alexandreberg/SAPI_an_open_source_FEWS/docs/tests/notifications-m4-m6/images/03_predictions_php_overview.png

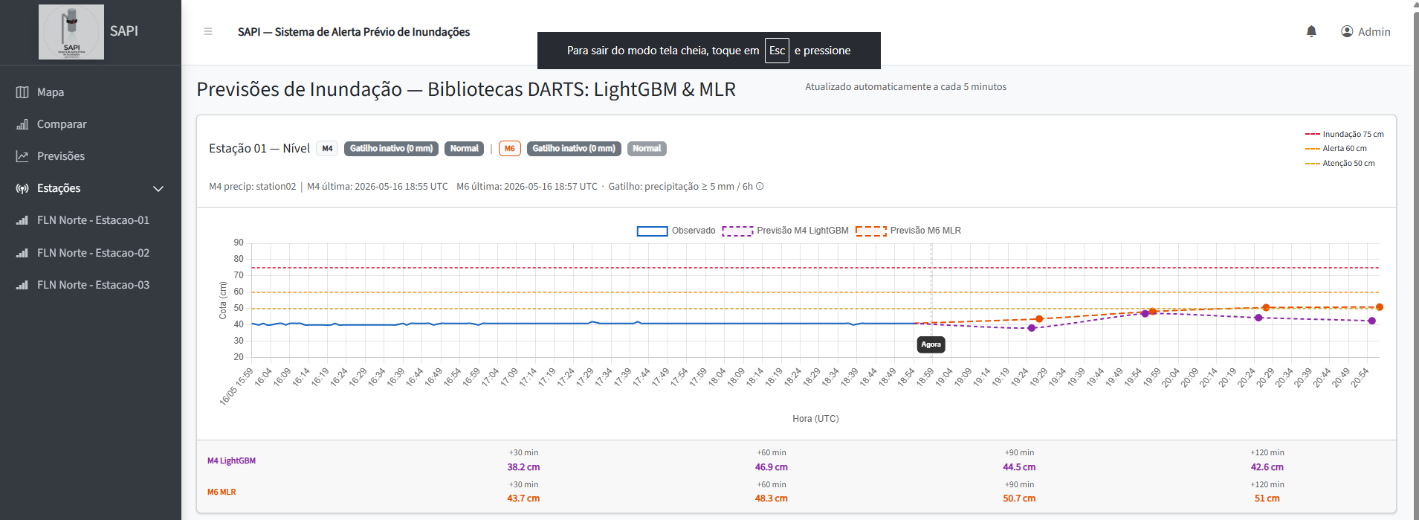
docs/tests/notifications-m4-m6/images/03_predictions_php_overview.png
