alexandreberg/SAPI_an_open_source_FEWS/hardware/lora-arduino-shield-v1.0/SAPI_LoRa_Arduino_Shield_V1.0-FC.png

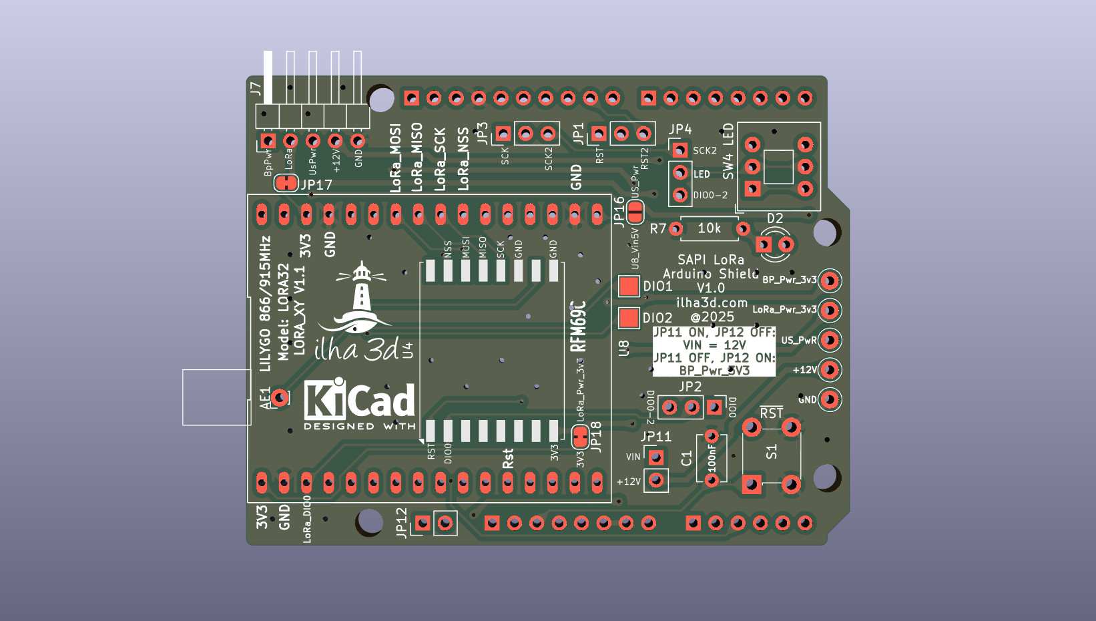
hardware/lora-arduino-shield-v1.0/SAPI_LoRa_Arduino_Shield_V1.0-FC.png
