alexandreberg/SAPI_an_open_source_FEWS/hardware/morpho-shield-v1.2/jlcpcb-02.11.2025.png

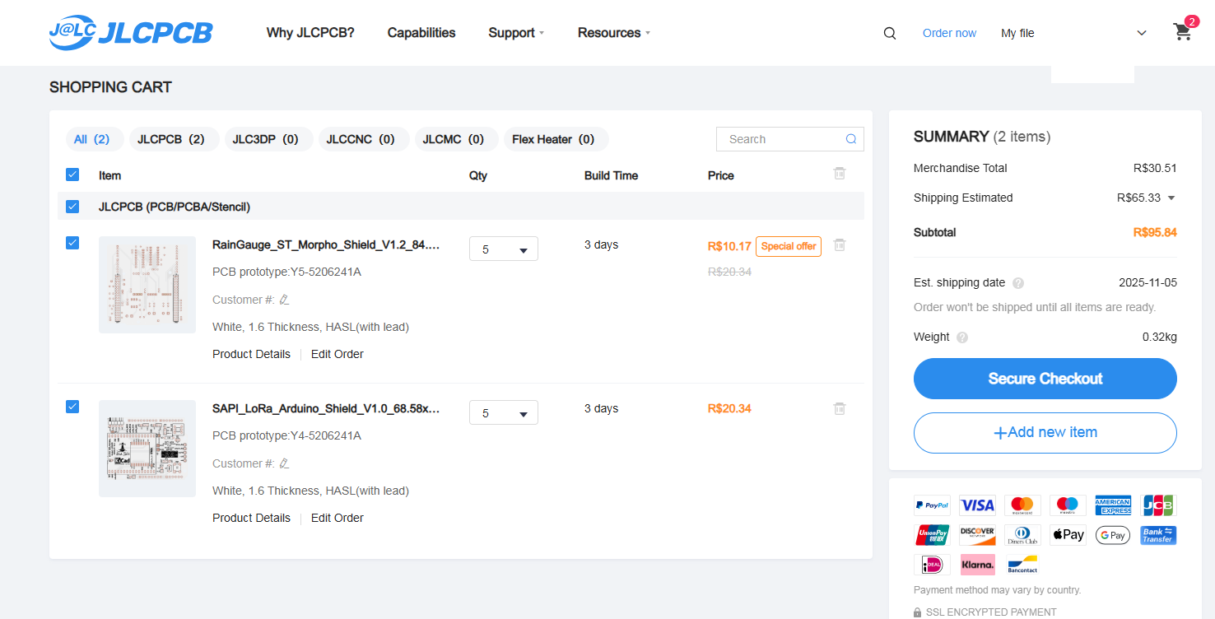
hardware/morpho-shield-v1.2/jlcpcb-02.11.2025.png
