alexandreberg/SAPI_an_open_source_FEWS/hardware/morpho-shield-v1.2/RainGauge_ST_Morpho_Shield_V1.2-BC-comp.png

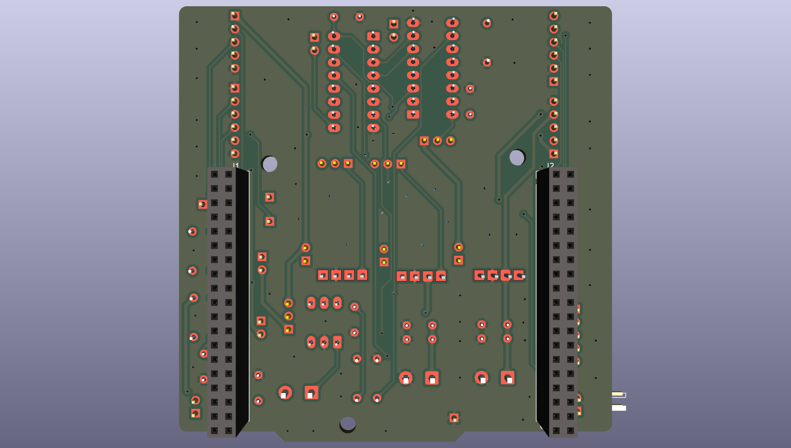
hardware/morpho-shield-v1.2/RainGauge_ST_Morpho_Shield_V1.2-BC-comp.png
