alexandreberg/SAPI_an_open_source_FEWS/webserver/public_html/sapi/assets/img/stations/station-1.jpg

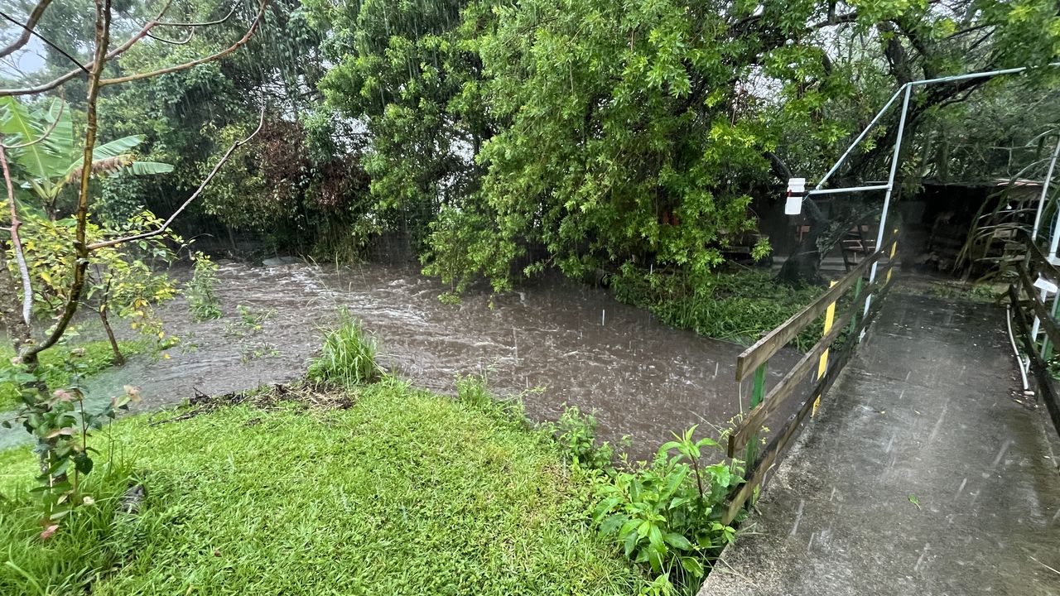
webserver/public_html/sapi/assets/img/stations/station-1.jpg
