alexandreberg/SAPI_an_open_source_FEWS/webserver/public_html/sapi/assets/img/stations/station-3.jpg

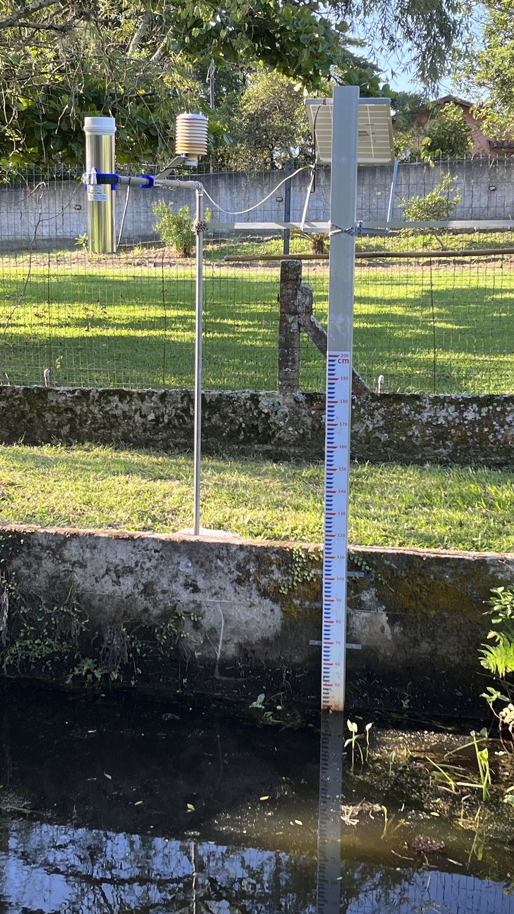
webserver/public_html/sapi/assets/img/stations/station-3.jpg
