alexandreberg/SAPI_an_open_source_FEWS/docs/tests/us-100/US-100_Trigger_Echo_mode_test-01/Data_test_US-100_Trigger_2026.Feb.15.md

## Test Results
Check that there is a problem. The US-100 in trigger mode is measuring at the maximum of 180cm.
Check for some code issue or it might be sensor specific problem?
I think it my be something with the filtering range routine.

**Note:** Bosch GLM 20 measurements corrected by -10.0 cm to account for instrument offset identified after testing.

* All measures in cm:
US-100 - Bosch (corrected)
28 - 25.7
48 - 44.0
68 - 63.1
98 - 89.7
126 - 115.3
152 - 139.3
180 - 164.2
-99 - 187.7
-99 - 209.3
-99 - 230.7
-99 - 248.9
-99 - 210.1
-99 - 200.1
-99 - 190.1
-99 - 187.7
-99 - 182.2
-99 - 175.9
-99 - 170.2
180 - 164.1
