alexandreberg/SAPI_an_open_source_FEWS/predictive-models/results_final_m4_lgbm/event_windows_v3.csv

event_num | peak_time | peak_cm | analysis_start | analysis_end | split_set | type | level | donor_pct | notes | exclusion | p24h_mm
1 | 2025-01-17 14:35:00 | 79 | 2025-01-16 21:45:00 | 2025-01-18 18:50:00 | train | flood | Alerta | 0.0 | subida máx. em 30 min: 7 cm |  | 192.6
2 | 2025-01-26 00:05:00 | 66 | 2025-01-25 17:55:00 | 2025-01-26 07:45:00 | train | flood | Atenção | 0.0 | subida máx. em 30 min: 6 cm |  | 52.5
3 | 2025-02-18 03:30:00 | 48 | 2025-02-17 22:10:00 | 2025-02-18 08:05:00 | train | flood | Normal | 0.0 | subida máx. em 30 min: 1 cm |  | 20.7
4 | 2025-04-10 19:35:00 | 98 | 2025-04-10 14:15:00 | 2025-04-11 22:55:00 | train | flash_flood | Inundação | 0.0 | subida máx. em 30 min: 34 cm |  | 5.3
5 | 2025-06-23 10:10:00 | 56 | 2025-06-23 03:55:00 | 2025-06-23 22:20:00 | train | flood | Normal | 0.0 | subida máx. em 30 min: 5 cm |  | 5.4
6 | 2025-06-26 22:25:00 | 58 | 2025-06-26 16:00:00 | 2025-06-27 09:00:00 | train | flood | Normal | 0.0 | subida máx. em 30 min: 6 cm |  | 6.9
7 | 2025-10-29 06:00:00 | 45 | 2025-10-29 00:55:00 | 2025-10-29 09:25:00 | train | flood | Normal | 0.0 | subida máx. em 30 min: 1 cm |  | 19.6
8 | 2025-12-09 15:00:00 | 163 | 2025-12-09 09:55:00 | 2025-12-10 18:35:00 | train | flash_flood | Inundação | 0.0 | subida máx. em 30 min: 78 cm |  | 31.5
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
32 | 2026-08-12 19:55:00 | 80 | 2026-08-12 11:40:00 | 2026-08-13 12:00:00 | test | flood | Alerta | 87.4 | subida máx. em 30 min: 9 cm; 87% da janela vem da E03 (Issue #225) |  | 48.6
33 | 2026-08-15 16:30:00 | 92 | 2026-08-13 14:55:00 | 2026-08-16 09:20:00 | test | flood | Inundação | 92.9 | subida máx. em 30 min: 11 cm; 93% da janela vem da E03 (Issue #225) |  | 56.5
34 | 2026-08-29 15:55:00 | 77 | 2026-08-29 10:30:00 | 2026-08-30 07:50:00 | test | flood | Alerta | 0.0 | subida máx. em 30 min: 12 cm |  | 22.0
35 | 2026-09-01 02:20:00 | 101 | 2026-08-30 09:10:00 | 2026-09-01 20:25:00 | test | flood | Inundação | 0.0 | subida máx. em 30 min: 11 cm |  | 54.7
