alexandreberg/SAPI_an_open_source_FEWS/predictive-models/results_final_m6_mlr/README.md

# results_final_m6_mlr

**Final validated backtesting for Model 6 — LinearRegressionModel / MLR (Darts).**

Previously named `real_data_m6_mlr/`. Contains the M6 backtest results and the controlled
M4 vs M6 comparison (same pipeline, same events, same thresholds — only the learning
algorithm differs) used in the dissertation methodology.

## Scripts

| Script | Purpose |
|---|---|
| `config.py` | Hyper-parameters — identical to `../results_final_m4_lgbm/config.py` and mirrored in `production_m6/config_production_m6.py`; `EVENTS_CSV` points to the shared `../results_final_m4_lgbm/event_windows_v3.csv` |
| `real_utils.py` | Data loading (identical pipeline to M4) |
| `01_model6_mlr_continuous.py` | Continuous backtest over the full record (2024-12-30 → 2026-09-12, ~21 months); auto-detects 25 Atenção-crossing periods |
| `02_precip_gate_m6.py` | Gate sensitivity (5/10/15 mm) |
| `03_compare_m4_m6.py` | M4 vs M6 comparison plot and metrics (`compare_m4_vs_m6.*`) |
| `04_lead_time_m6.py` | Lead time analysis by alert level |
| `05_rmse_per_event.py` | RMSE per test event, M4 vs M6 (`rmse_per_event*`) |
| `06_compare_fullsim.py` | RMSE over the full continuous simulation (`compare_m4_vs_m6_fullsim.*`) |

## Output images (`output/`)

**Summary M4-vs-M6 comparison:**
- `compare_m4_vs_m6.png` — RMSE per horizon and alert metrics (recall / false positives)
  at 60/75/90 cm, gate 5 mm / 6 h, persistence of 3 steps. **Read the caveat below.**
- `compare_m4_vs_m6_fullsim.png` — RMSE over the full continuous simulation, same caveat
- `lead_time_comparison_m4_vs_m6.png` — advance warning time by level, per test event
  (E28–E37) and horizon
- `rmse_per_event_m4_vs_m6.png` — RMSE per test event

**Per model:**
- `lead_time_atencao_m6.png`, `lead_time_alerta_m6.png`, `lead_time_inundacao_m6.png`
- `alert_timeline_atencao.png` / `alert_timeline_alerta.png` / `alert_timeline_inundacao.png`
- `precip_gate_timeline_[level]_gate[5/10/15]mm.png` — 9 images (gate analysis)

**Per auto-detected period** (from the continuous backtest, distinct from the 37 catalogued
episodes in `event_windows_v3.csv` — see Issue #213):
- `event_detected_001.png` … `event_detected_025.png` — numbered identically to
  `results_final_m4_lgbm/output/`'s plots (same observed level, threshold and merge gap drive
  `detect_flood_periods()` for both models). See the
  [period → catalogued event mapping table](../results_final_m4_lgbm/README.md#auto-detected-period--catalogued-event-mapping)
  in the M4 README for which `NNN` corresponds to which `Exx`.

## Caveat — which numbers are the published ones

`compare_m4_vs_m6.png` and `compare_m4_vs_m6_fullsim.png` compute the RMSE over **every step of
the record**, so they mix the training period (~79 % of the record, where the flexible M4 fits
much better) with the test period, and their alert counts include the training events. They do
**not** reproduce the dissertation's RMSE table, which reports the **out-of-sample** (test,
from 2026-05-01) and in-sample values separately, nor its test-only detection table. The
`lead_time_comparison_m4_vs_m6.png` figure, in contrast, covers the test events only.
Any claim about relative model performance must use the out-of-sample numbers in
the dissertation (authoritative) or the audit report generated by
`../plot_events_audit_pdf.py` (`../output_audit/auditoria_eventos_A3.pdf`).

## Documentation

- ~~`model6_comparison_pt-BR.md` / `.pdf`~~ — archived in the development repository on 2026-09-12:
  the deck dates from 2026-05-25 and still cites the 50/60/75 cm thresholds and the v2
  catalogue. Current numbers are in the
  dissertation and the audit report.

## Related

- M4 results: `../results_final_m4_lgbm/`
- Production config: `../production_m6/config_production_m6.py`
