alexandreberg/SAPI_an_open_source_FEWS/docs/tests/us-100/US-100_Serial_mode_test-02/Test-02-readings.md

## US-100 Serial Mode Measurement Test-02
Repeated test with US-100 in Serial mode in the new environment (dame pictures used in trigger mode), only with jumper inserted

**Note:** Bosch GLM 20 measurements corrected by -10.0 cm to account for instrument offset identified after testing.

* All measurements are in cm.

US-100 | Bosch (corrected)
27 | 24.0
43 | 39.9
58 | 54.0
71 | 66.2
90 | 84.7
107 | 101.1
121 | 113.9
139 | 130.8
159 | 148.7
175 | 163.7
197 | 183.4
222 | 207.2
243 | 225.9
268 | 249.4
294 | 274.1
315 | 292.7
333 | 309.4
355 | 329.0
371 | 344.7
395 | 367.1
-99 | 385.6
439 | 406.0
-99 | 419.0
-99 | 437.1
-99 | 451.3
-99 | 427.7
435 | 402.0
-99 | 391.4
408 | 378.6
396 | 367.3
385 | 356.7
366 | 339.5
348 | 322.7
328 | 304.3
310 | 288.3
285 | 265.2
265 | 247.0
244 | 227.2
223 | 207.3
201 | 187.9
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

Repeat the analysis from the first test in serial mode to this one and check if the results are consistent. After that create the report.
