alexandreberg/SAPI_an_open_source_FEWS/predictive-models/results_final_m4_lgbm/output/alert_analysis.csv

threshold_name | threshold_cm | debounce_steps | debounce_min | VP | FP | FN | VN | precision | recall | F1
Atenção | 60 | 1 | 5 | 18 | 25 | 0 | 169516 | 0.419 | 1.0 | 0.59
Atenção | 60 | 2 | 10 | 18 | 14 | 0 | 169603 | 0.562 | 1.0 | 0.72
Atenção | 60 | 3 | 15 | 18 | 9 | 0 | 169664 | 0.667 | 1.0 | 0.8
Alerta | 75 | 1 | 5 | 11 | 3 | 0 | 173126 | 0.786 | 1.0 | 0.88
Alerta | 75 | 2 | 10 | 11 | 3 | 0 | 173174 | 0.786 | 1.0 | 0.88
Alerta | 75 | 3 | 15 | 10 | 3 | 1 | 173213 | 0.769 | 0.909 | 0.833
Inundação | 90 | 1 | 5 | 6 | 0 | 1 | 175329 | 1.0 | 0.857 | 0.923
Inundação | 90 | 2 | 10 | 6 | 0 | 1 | 175343 | 1.0 | 0.857 | 0.923
Inundação | 90 | 3 | 15 | 6 | 0 | 1 | 175356 | 1.0 | 0.857 | 0.923
