alexandreberg/SAPI_an_open_source_FEWS/predictive-models/results_final_m4_lgbm/output/lead_time_summary_m4.csv

event_num | peak_cm | threshold_name | threshold_cm | occurrence | n_occurrences | t_obs | at_window_start | search_start | search_end | fire_30min | lead_time_30min | active_30min | fire_60min | lead_time_60min | active_60min | fire_90min | lead_time_90min | active_90min | fire_120min | lead_time_120min | active_120min
28 | 60.0 | Atenção | 60 | 1 | 1 | 2026-06-20 21:30:00 | False | 2026-06-20 18:30:00 | 2026-06-20 23:30:00 |  |  | False |  |  | False | 2026-06-20 21:15:00 | 15.0 | False | 2026-06-20 20:40:00 | 50.0 | False
29 | 65.0 | Atenção | 60 | 1 | 1 | 2026-06-30 09:55:00 | False | 2026-06-30 06:55:00 | 2026-06-30 19:30:00 | 2026-06-30 10:10:00 | -15.0 | False | 2026-06-30 10:10:00 | -15.0 | False | 2026-06-30 09:45:00 | 10.0 | False | 2026-06-30 09:30:00 | 25.0 | False
30 | 61.0 | Atenção | 60 | 1 | 1 | 2026-07-01 12:15:00 | False | 2026-07-01 09:15:00 | 2026-07-01 18:45:00 | 2026-07-01 13:35:00 | -80.0 | False |  |  | False |  |  | False |  |  | False
31 | 97.0 | Atenção | 60 | 1 | 1 | 2026-07-11 12:00:00 | False | 2026-07-11 09:00:00 | 2026-07-12 13:40:00 | 2026-07-11 12:05:00 | -5.0 | False | 2026-07-11 12:05:00 | -5.0 | False | 2026-07-11 11:55:00 | 5.0 | False | 2026-07-11 11:50:00 | 10.0 | False
32 | 80.0 | Atenção | 60 | 1 | 1 | 2026-08-12 16:30:00 | False | 2026-08-12 13:30:00 | 2026-08-13 05:50:00 | 2026-08-12 16:30:00 | 0.0 | False | 2026-08-12 16:25:00 | 5.0 | False | 2026-08-12 16:30:00 | 0.0 | False | 2026-08-12 16:25:00 | 5.0 | False
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
37 | 100.0 | Inundação | 90 | 1 | 1 | 2026-09-11 16:25:00 | False | 2026-09-11 13:25:00 | 2026-09-11 21:50:00 | 2026-09-11 17:15:00 | -50.0 | False |  |  | False |  |  | False |  |  | False
