alexandreberg/SAPI_an_open_source_FEWS/predictive-models/results_final_m4_lgbm/output/precip_gate_analysis.csv

threshold_name | threshold_cm | gate_hours | gate_mm | debounce_steps | debounce_min | VP | FP | FN | VN | precision | recall | F1
Atenção | 60 | 6 | 0 | 1 | 5 | 18 | 25 | 0 | 169516 | 0.419 | 1.0 | 0.59
Atenção | 60 | 6 | 0 | 2 | 10 | 18 | 14 | 0 | 169603 | 0.562 | 1.0 | 0.72
Atenção | 60 | 6 | 0 | 3 | 15 | 18 | 9 | 0 | 169664 | 0.667 | 1.0 | 0.8
Alerta | 75 | 6 | 0 | 1 | 5 | 11 | 3 | 0 | 173126 | 0.786 | 1.0 | 0.88
Alerta | 75 | 6 | 0 | 2 | 10 | 11 | 3 | 0 | 173174 | 0.786 | 1.0 | 0.88
Alerta | 75 | 6 | 0 | 3 | 15 | 10 | 3 | 1 | 173213 | 0.769 | 0.909 | 0.833
Inundação | 90 | 6 | 0 | 1 | 5 | 6 | 0 | 1 | 175329 | 1.0 | 0.857 | 0.923
Inundação | 90 | 6 | 0 | 2 | 10 | 6 | 0 | 1 | 175343 | 1.0 | 0.857 | 0.923
Inundação | 90 | 6 | 0 | 3 | 15 | 6 | 0 | 1 | 175356 | 1.0 | 0.857 | 0.923
Atenção | 60 | 6 | 5 | 1 | 5 | 18 | 8 | 0 | 170215 | 0.692 | 1.0 | 0.818
Atenção | 60 | 6 | 5 | 2 | 10 | 18 | 2 | 0 | 170277 | 0.9 | 1.0 | 0.947
Atenção | 60 | 6 | 5 | 3 | 15 | 18 | 0 | 0 | 170321 | 1.0 | 1.0 | 1.0
Alerta | 75 | 6 | 5 | 1 | 5 | 11 | 0 | 0 | 173188 | 1.0 | 1.0 | 1.0
Alerta | 75 | 6 | 5 | 2 | 10 | 11 | 0 | 0 | 173232 | 1.0 | 1.0 | 1.0
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
