alexandreberg/SAPI_an_open_source_FEWS/predictive-models/results_final_m6_mlr/output/compare_m4_vs_m6_fullsim.csv

horizonte_min | REQM_M4_LightGBM_cm | REQM_M6_MLR_cm
30 | 1.04 | 0.974
60 | 1.469 | 1.528
90 | 1.704 | 1.948
120 | 1.909 | 2.259
