alexandreberg/SAPI_an_open_source_FEWS/docs/tests/us-100/US-100_Serial_mode_test-01/US-100_Serial_Mode_Test-04.JPG

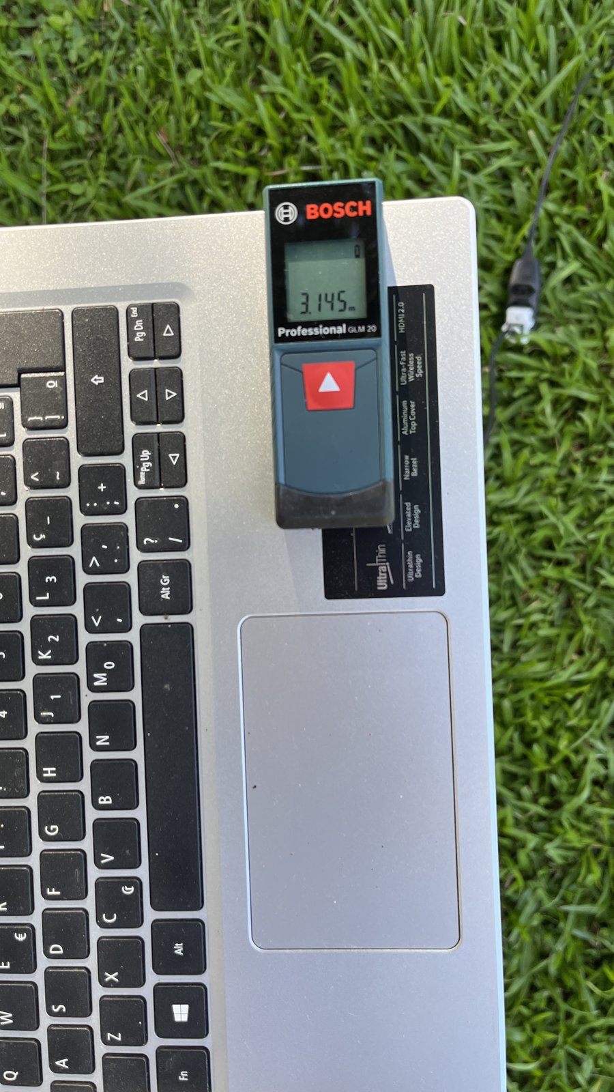
docs/tests/us-100/US-100_Serial_mode_test-01/US-100_Serial_Mode_Test-04.JPG
