alexandreberg/SAPI_an_open_source_FEWS/docs/tests/us-100/US-100_Serial_mode_test-04/images/IMG_3337.JPG

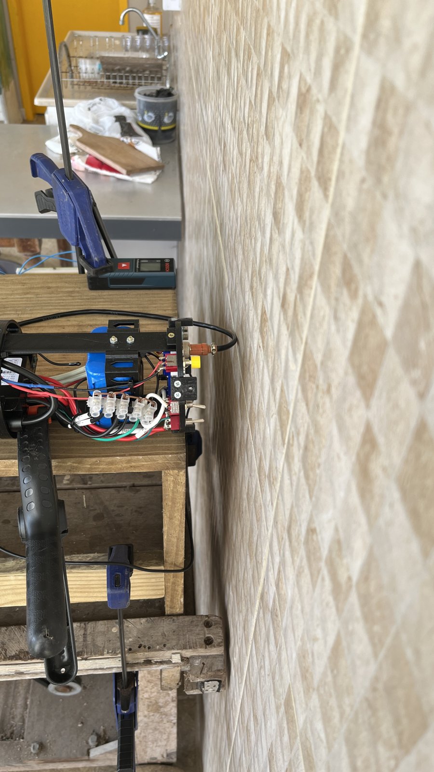
docs/tests/us-100/US-100_Serial_mode_test-04/images/IMG_3337.JPG
