alexandreberg/SAPI_an_open_source_FEWS/predictive-models/results_final_m4_lgbm/output/alert_timeline_atencao.png

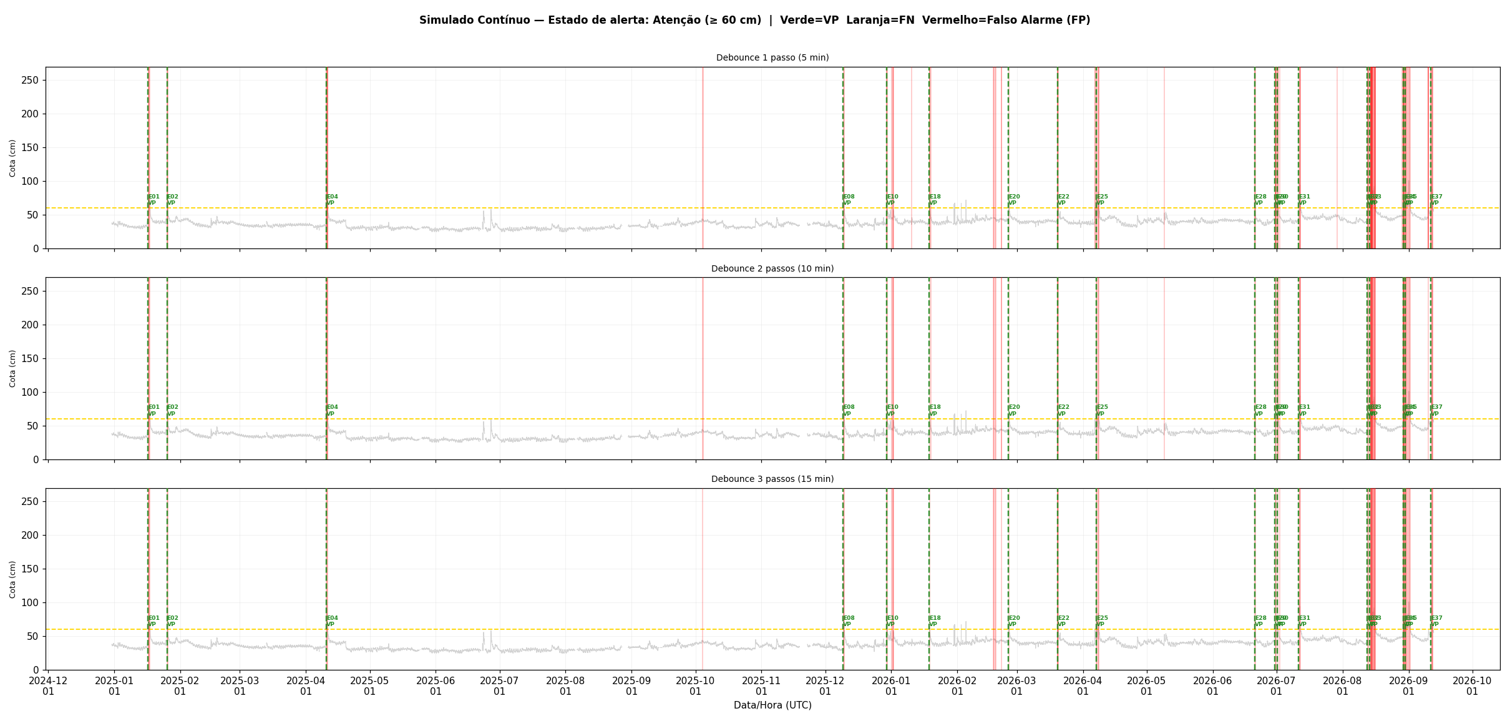
predictive-models/results_final_m4_lgbm/output/alert_timeline_atencao.png
