alexandreberg/SAPI_an_open_source_FEWS/predictive-models/results_final_m4_lgbm/output/event_detected_006.png

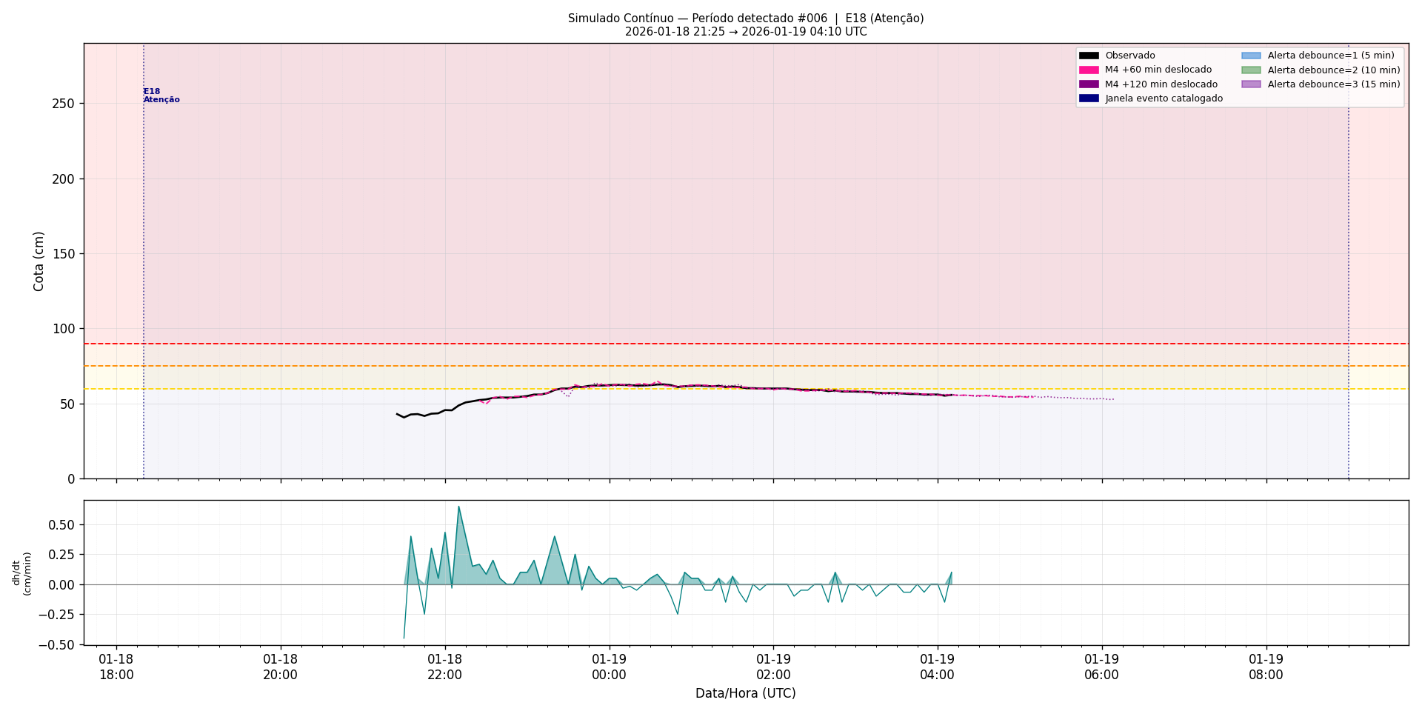
predictive-models/results_final_m4_lgbm/output/event_detected_006.png
