alexandreberg/SAPI_an_open_source_FEWS/predictive-models/results_final_m4_lgbm/output/lead_time_alerta_m4.png

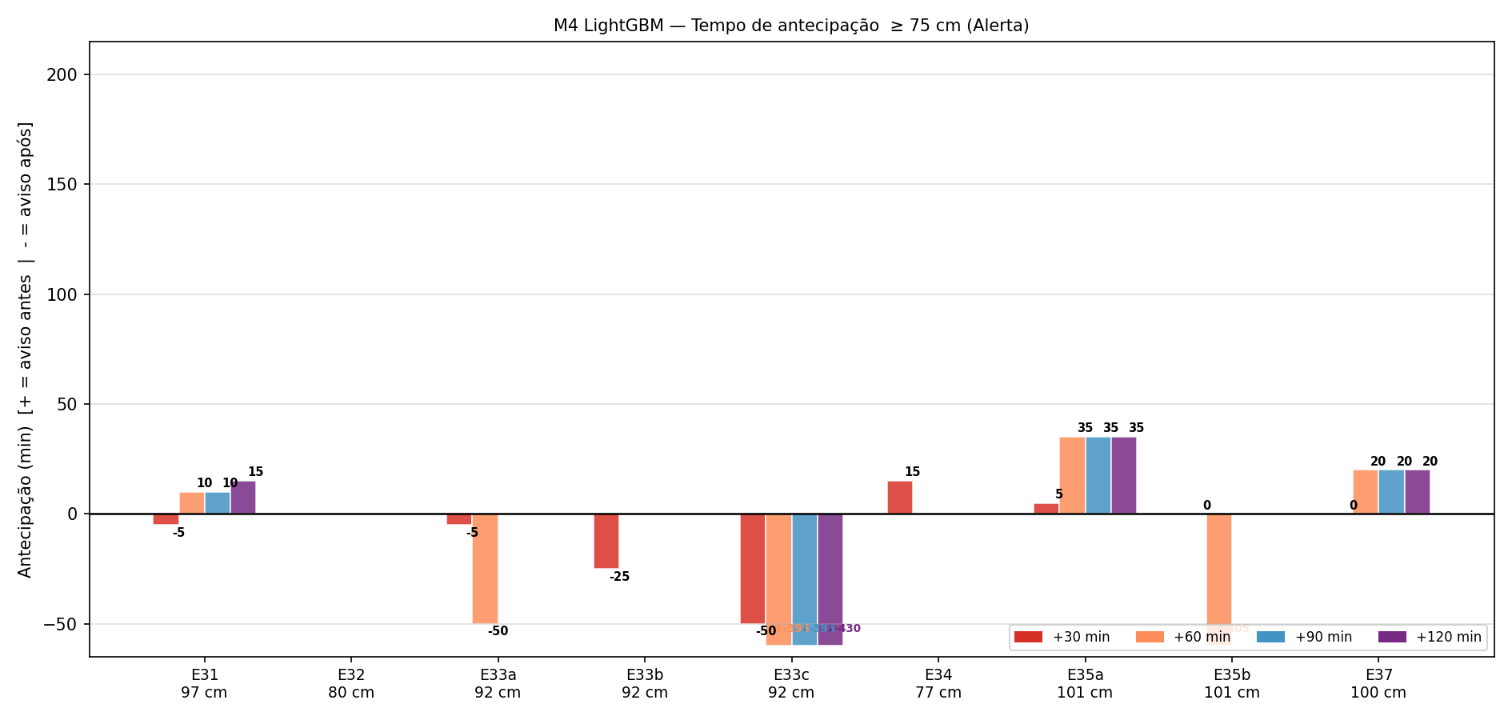
predictive-models/results_final_m4_lgbm/output/lead_time_alerta_m4.png
