alexandreberg/SAPI_an_open_source_FEWS/predictive-models/results_final_m4_lgbm/output/precip_gate_timeline_alerta_gate5mm.png

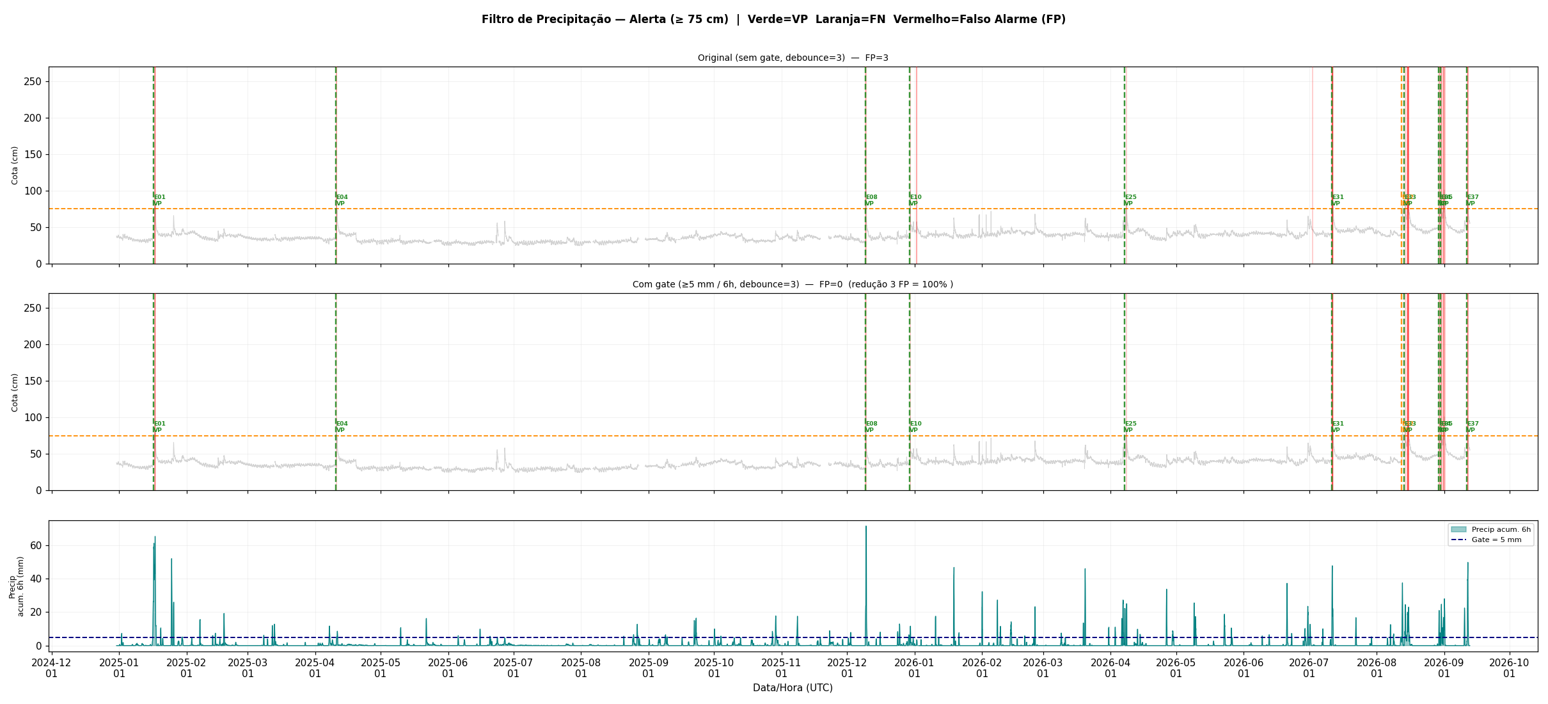
predictive-models/results_final_m4_lgbm/output/precip_gate_timeline_alerta_gate5mm.png
