alexandreberg/SAPI_an_open_source_FEWS/predictive-models/results_final_m6_mlr/output/alert_timeline_atencao.png

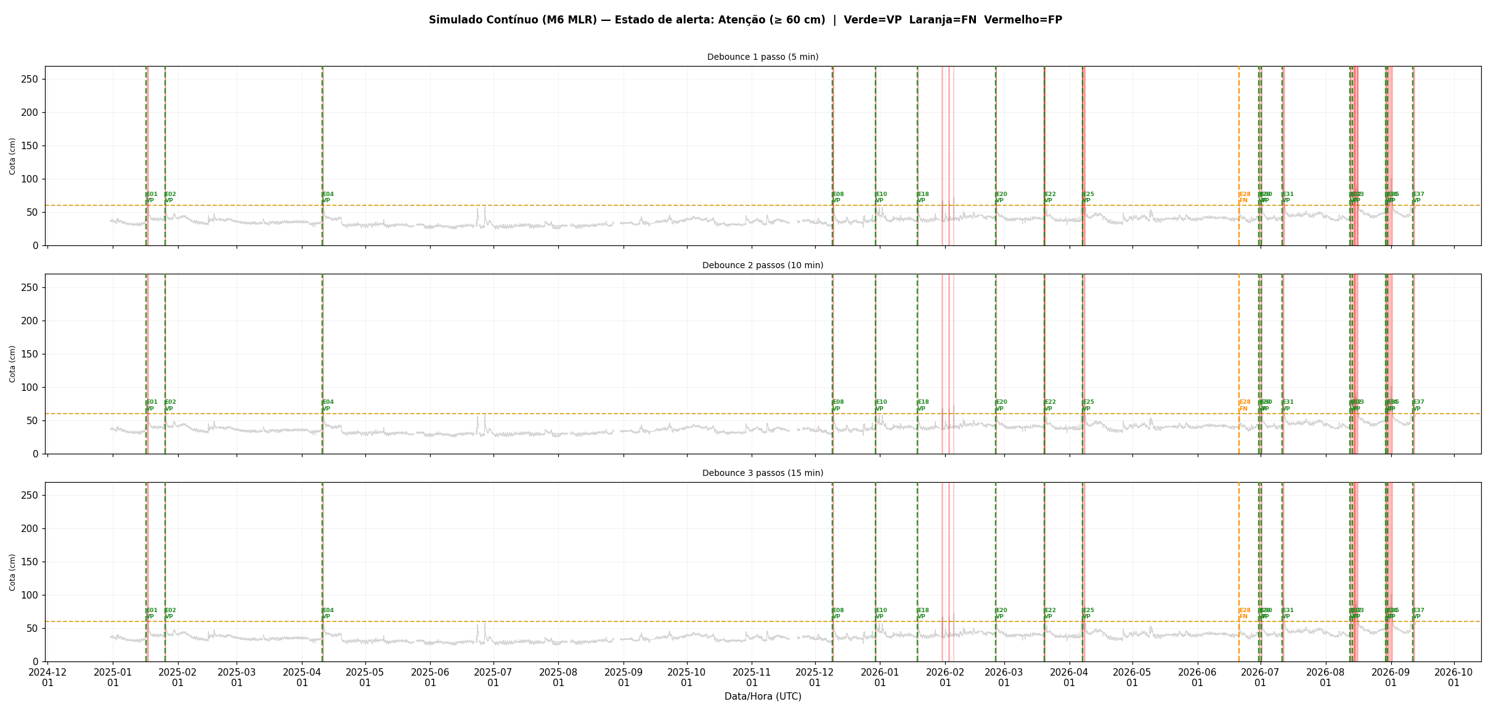
predictive-models/results_final_m6_mlr/output/alert_timeline_atencao.png
