alexandreberg/SAPI_an_open_source_FEWS/predictive-models/results_final_m6_mlr/output/event_detected_003.png

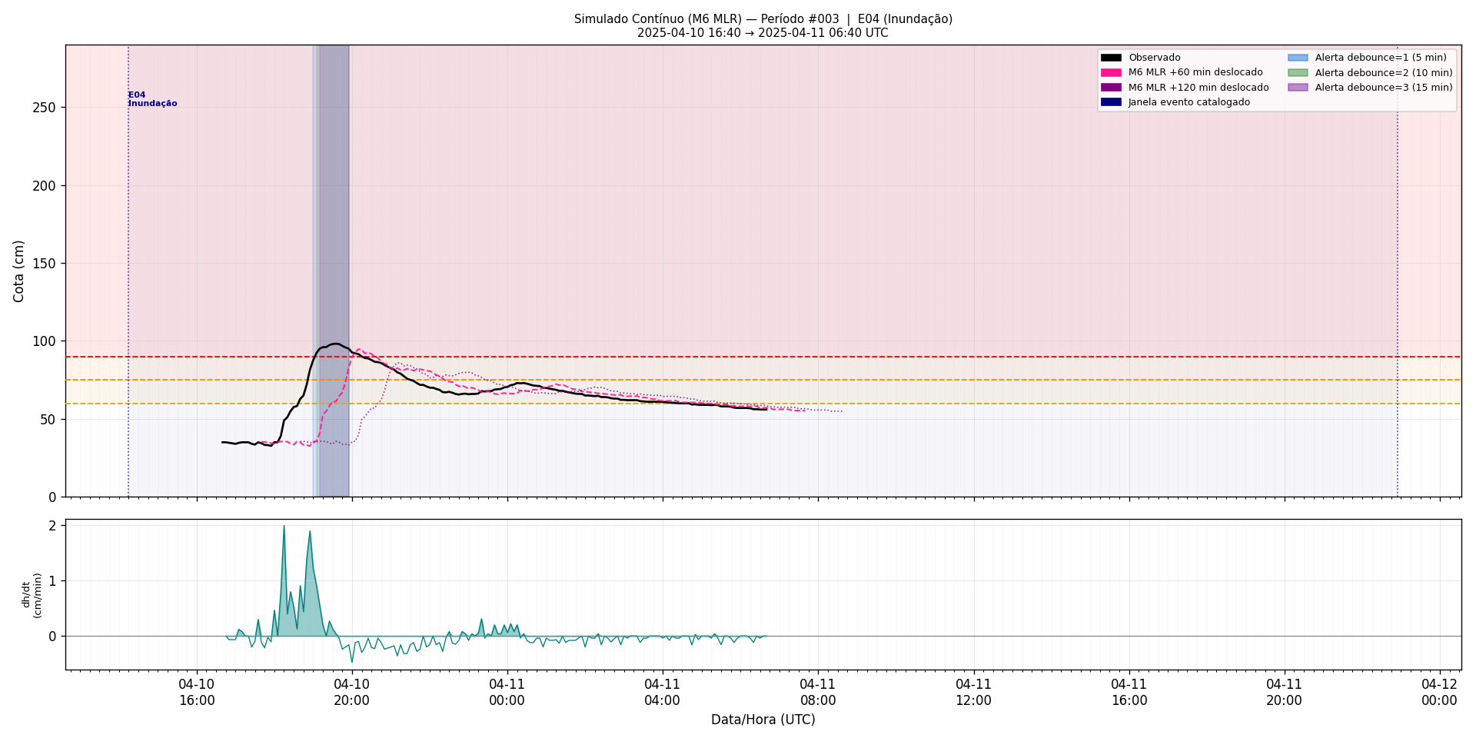
predictive-models/results_final_m6_mlr/output/event_detected_003.png
