alexandreberg/SAPI_an_open_source_FEWS/predictive-models/results_final_m6_mlr/output/lead_time_comparison_m4_vs_m6.png

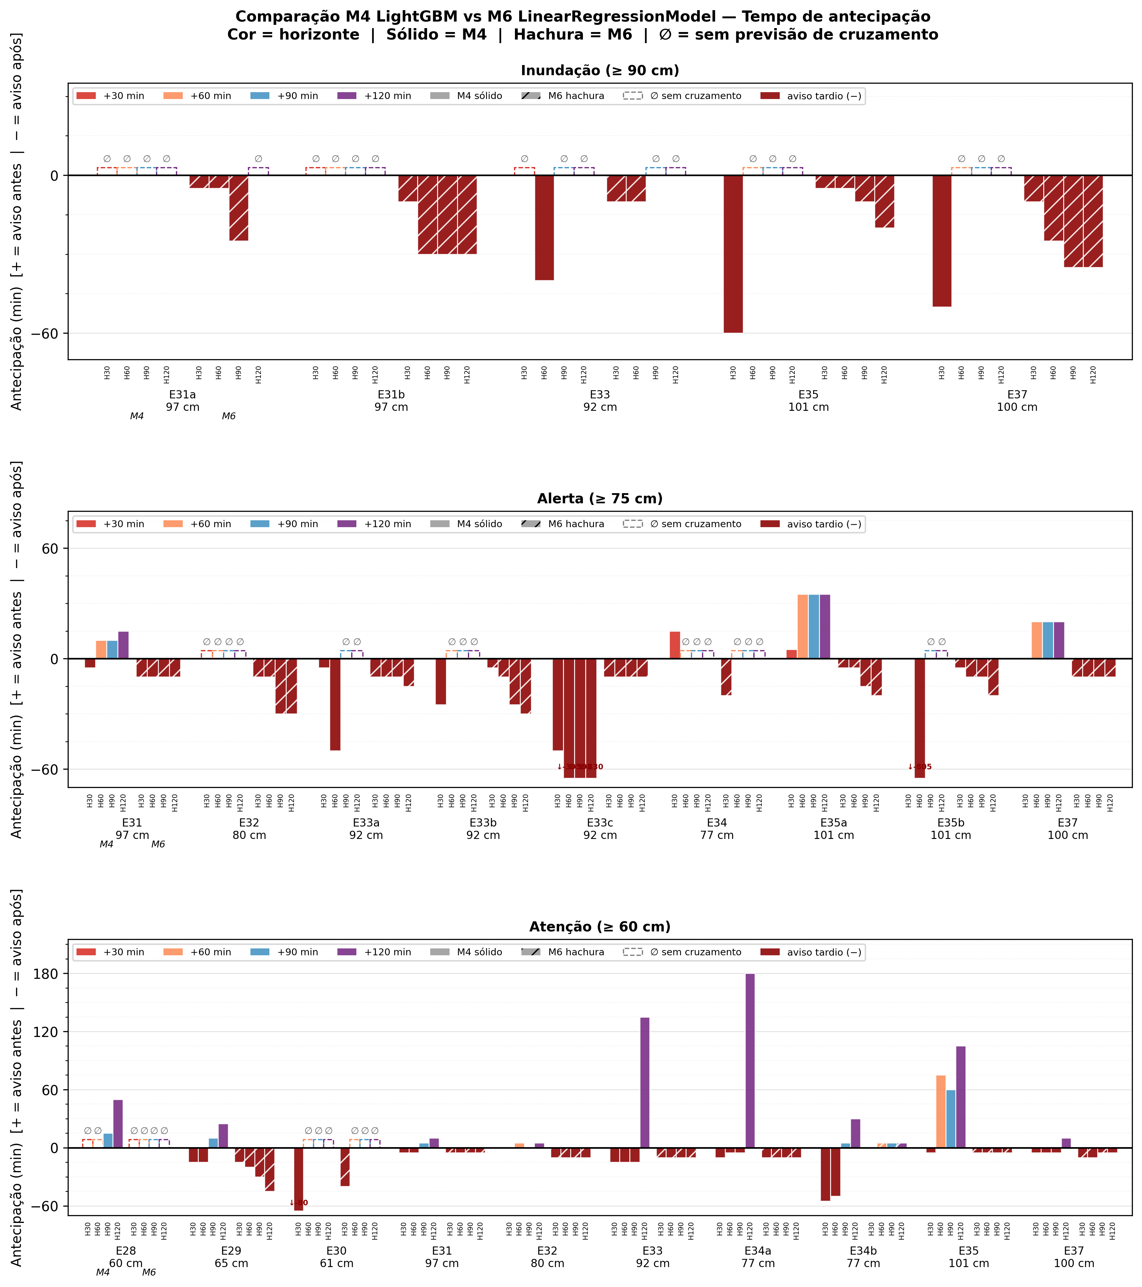
predictive-models/results_final_m6_mlr/output/lead_time_comparison_m4_vs_m6.png
