alexandreberg/SAPI_an_open_source_FEWS/predictive-models/results_final_m6_mlr/output/precip_gate_timeline_atencao_gate15mm.png

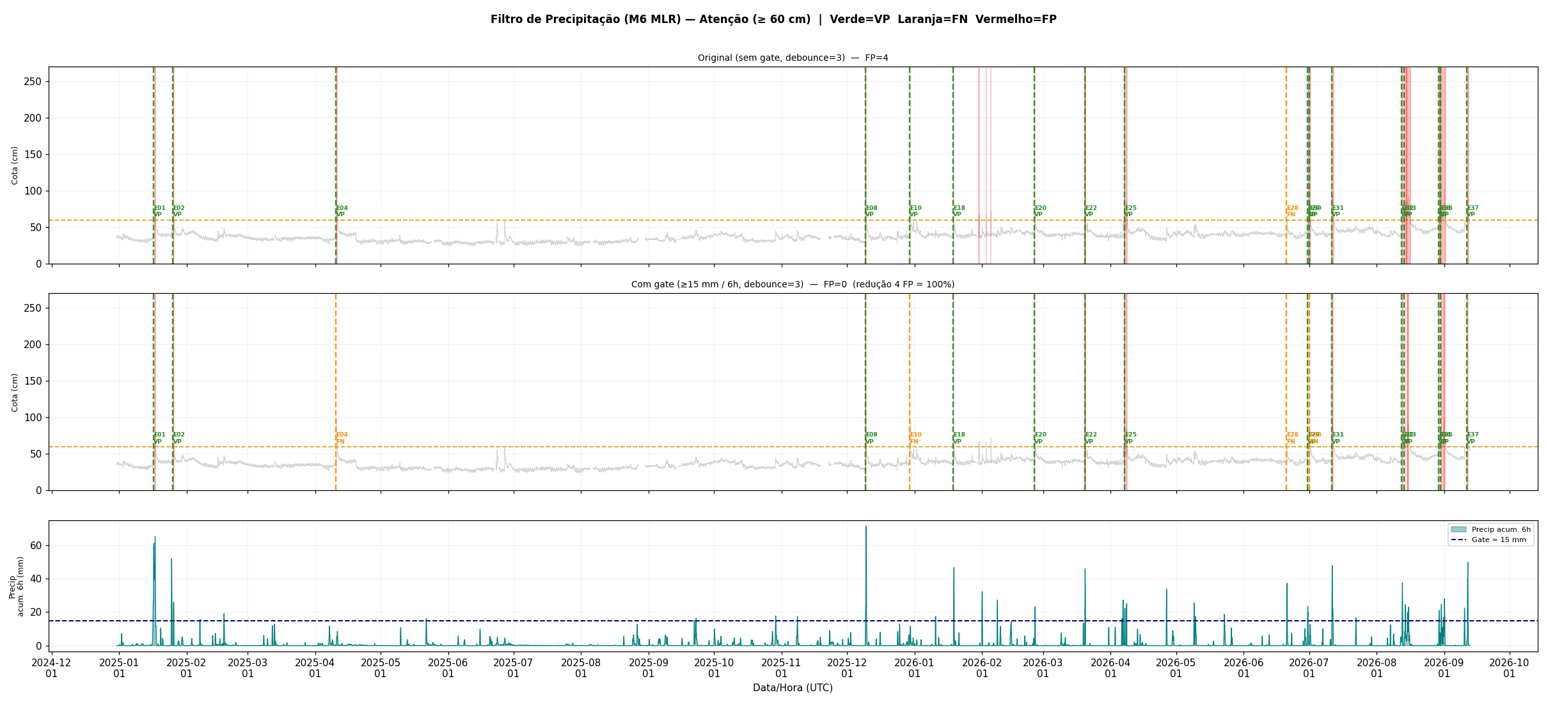
predictive-models/results_final_m6_mlr/output/precip_gate_timeline_atencao_gate15mm.png
