alexandreberg/SAPI_an_open_source_FEWS/firmware/station-02/src/adc.cpp

/**
 * @file adc.cpp
 * @brief Implementation of ADC voltage measurement functions
 *
 * SPDX-License-Identifier: AGPL-3.0-or-later
 * Copyright (C) 2024–2026 Alexandre Nuernberg <alexandreberg@gmail.com>
 *
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
 * You should have received a copy of the GNU Affero General Public License
 * along with this program. If not, see <https://www.gnu.org/licenses/>.
 */

#include "adc.h"

/* ADC pins */
#define PIN_VBAT PC1 // ADC A4
#define PIN_PANEL PC0 // ADC A5

/* ADC configuration */
static const float ADC_MAX = 4095.0f;   // 12-bit ADC
static const float VREF    = 3.298f;    /* This value should be meaured on the board with a multimeter and updated here for better precision
                                         Measured reference voltage (3.3V rail) */

/* Voltage divider resistors (measured values) 
The resistor values in the board should be measured with a multimeter and updated here for better precision */
// Battery measurement (12V)
static const float R1_VBAT = 473700.0f; // High-side resistor (Ohms)
static const float R2_VBAT = 149790.0f; // Low-side resistor (Ohms)

// Solar panel measurement (20V)
static const float R1_PANEL = 694800.0f; // High-side resistor (Ohms)
static const float R2_PANEL = 102040.0f; // Low-side resistor (Ohms)

/**
 * @brief Initialize ADC subsystem
 */
void adc_init() {
    analogReadResolution(12);   // ADC resolution 12 bits (0 to 4095)
}

/**
 * @brief Read battery and solar panel voltages
 */
bool adc_read(adc_readings_t *readings) {
    if (readings == nullptr) {
        Serial.println("ERROR: Invalid pointer in adc_read()");
        return false;
    }

    /* Raw ADC readings */
    readings->rawBattery = analogRead(PIN_VBAT);
    readings->rawPanel   = analogRead(PIN_PANEL);

    /* Voltage at ADC pins */
    readings->adcVoltageBattery =
        (readings->rawBattery / ADC_MAX) * VREF;

    readings->adcVoltagePanel =
        (readings->rawPanel / ADC_MAX) * VREF;

    /* Voltage divider ratios */
    const float dividerBattery = (R1_VBAT + R2_VBAT) / R2_VBAT;
    const float dividerPanel  = (R1_PANEL + R2_PANEL) / R2_PANEL;

    /* Calculated real voltages */
    readings->batteryVoltage =
        readings->adcVoltageBattery * dividerBattery;

    readings->panelVoltage =
        readings->adcVoltagePanel * dividerPanel;

    return true;
}

/**
 * @brief Print ADC readings to serial output
 */
void adc_printReadings(const adc_readings_t *readings) {
    if (readings == nullptr) {
        Serial.println("ERROR: Invalid pointer in adc_printReadings()");
        return;
    }

    // Serial.print("ADC Raw Value (Battery): ");
    // Serial.println(readings->rawBattery);

    // Serial.print("Voltage at Battery ADC Pin: ");
    // Serial.print(readings->adcVoltageBattery, 3);
    // Serial.println(" V");

    Serial.print("Battery Voltage (calculated): ");
    Serial.print(readings->batteryVoltage, 2);
    Serial.println(" V");

    // Serial.print("ADC Raw Value (Solar Panel): ");
    // Serial.println(readings->rawPanel);

    // Serial.print("Voltage at Panel ADC Pin: ");
    // Serial.print(readings->adcVoltagePanel, 3);
    // Serial.println(" V");

    Serial.print("Solar Panel Voltage (calculated): ");
    Serial.print(readings->panelVoltage, 2);
    Serial.println(" V");

    Serial.println("---------------------------------------------");
}
